jasinai/plant_guard/presentation_0516/pics/IMAG0550.jpg

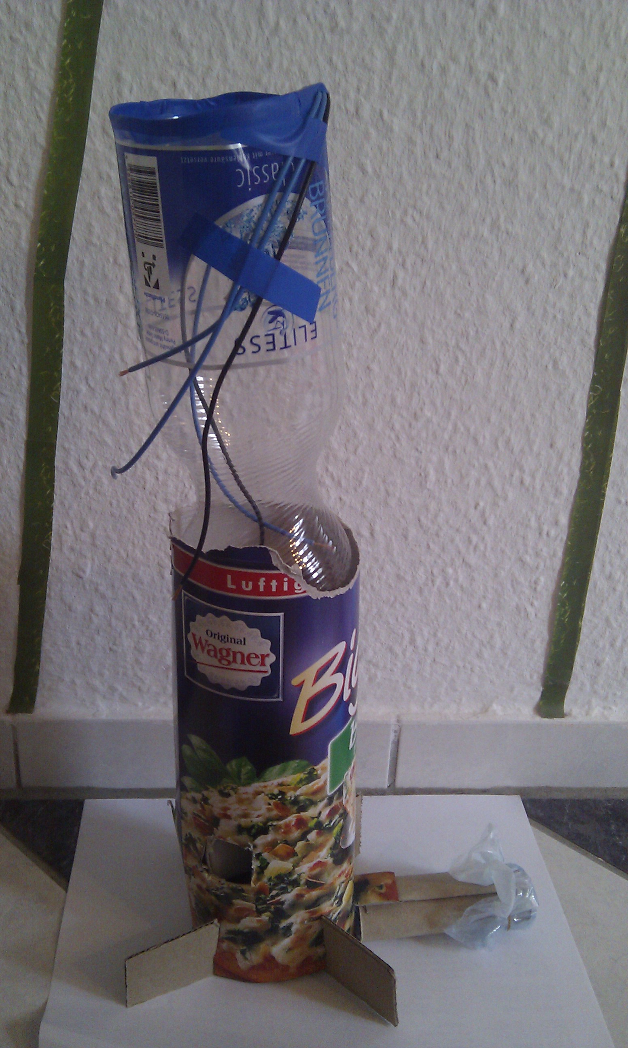
presentation_0516/pics/IMAG0550.jpg
