jasinai/plant_guard/presentation_0516/pics/IMAG0551.jpg

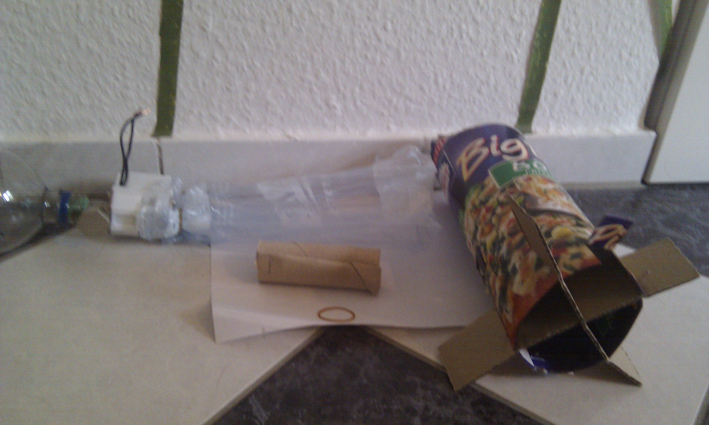
presentation_0516/pics/IMAG0551.jpg
